rbaron/b-parasite/img/orig/img3.jpg

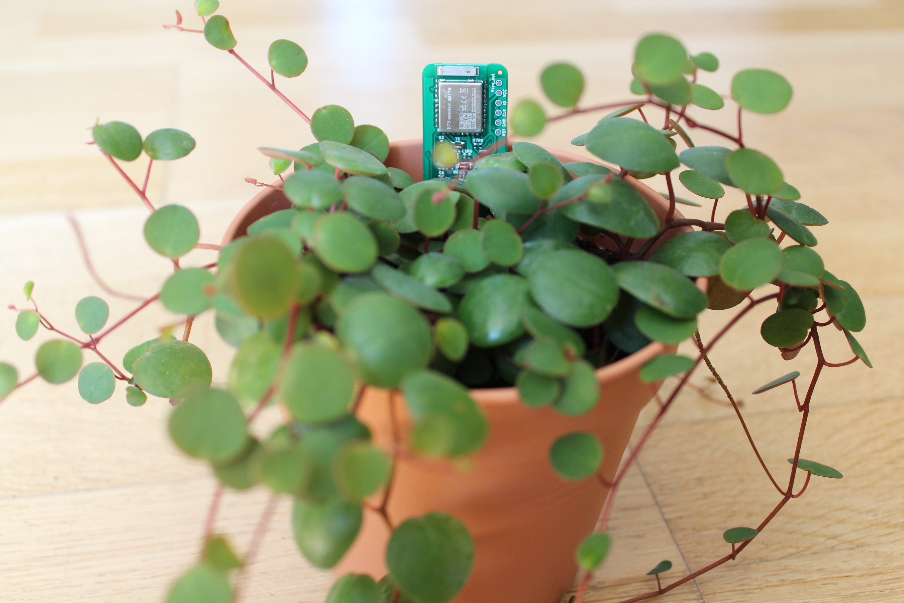
img/orig/img3.jpg
