rbaron/b-parasite/img/resized/img1.jpg

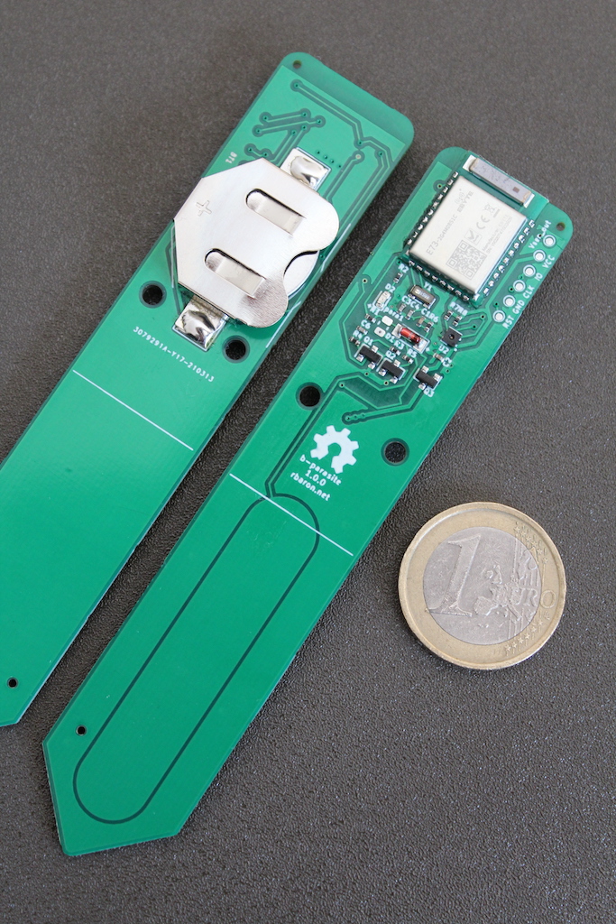
img/resized/img1.jpg
