rbaron/b-parasite/img/scope/0dbm-across-10ohm.png

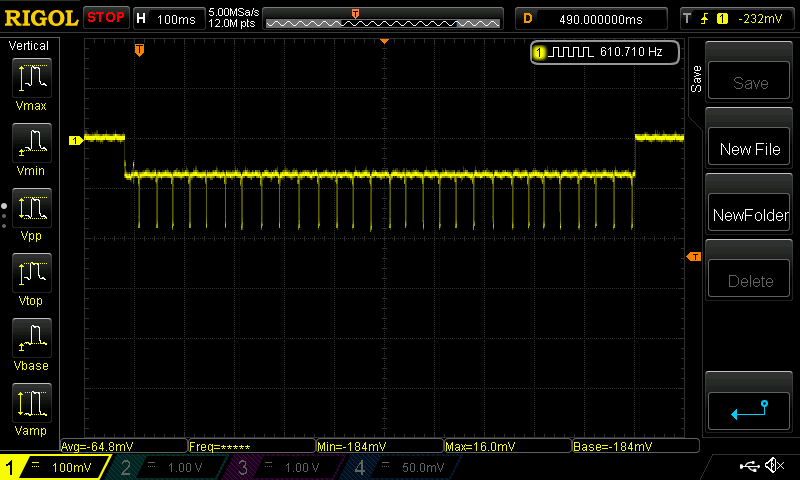
img/scope/0dbm-across-10ohm.png
